bluetiger9/nRF53-Wearable/Software/nrf5340_cpuapp/src/main_ble.c

#include "main_ble.h"

struct bt_conn *default_conn;

void connected(struct bt_conn *conn, uint8_t err)
{
	if (err) {
		printk("Connection failed (err 0x%02x)\n", err);
	} else {
		default_conn = bt_conn_ref(conn);
		printk("Connected\n");
	}
}

void disconnected(struct bt_conn *conn, uint8_t reason)
{
	printk("Disconnected (reason 0x%02x)\n", reason);

	if (default_conn) {
		bt_conn_unref(default_conn);
		default_conn = NULL;
	}
}

void bt_ready(void)
{
	int err;

	printk("Bluetooth initialized\n");

	err = bt_le_adv_start(BT_LE_ADV_CONN_NAME, ad, ARRAY_SIZE(ad), NULL, 0);
	if (err) {
		printk("Advertising failed to start (err %d)\n", err);
		return;
	}

	printk("Advertising successfully started\n");
}

void auth_cancel(struct bt_conn *conn)
{
	char addr[BT_ADDR_LE_STR_LEN];

	bt_addr_le_to_str(bt_conn_get_dst(conn), addr, sizeof(addr));

	printk("Pairing cancelled: %s\n", addr);
}

void bas_notify(void)
{
	uint8_t battery_level = bt_bas_get_battery_level();

	battery_level--;

	if (!battery_level) {
		battery_level = 100U;
	}

	bt_bas_set_battery_level(battery_level);
}

void hrs_notify(void)
{
	static uint8_t heartrate = 90U;

	/* Heartrate measurements simulation */
        heartrate = (int) get_heartrate();
	//heartrate++;
	//if (heartrate == 160U) {
        //    heartrate = 90U;
	//}

	bt_hrs_notify(heartrate);
}
